djtersteegc/fujinet-appleii-hardware/docs/SmartPort-IIC-Back.jpg

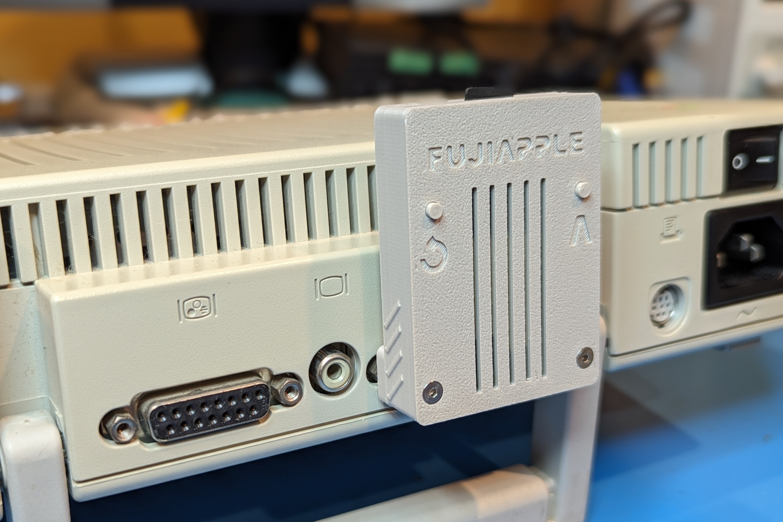
docs/SmartPort-IIC-Back.jpg
