djtersteegc/fujinet-appleii-hardware/docs/SmartPort-IIGS.jpg

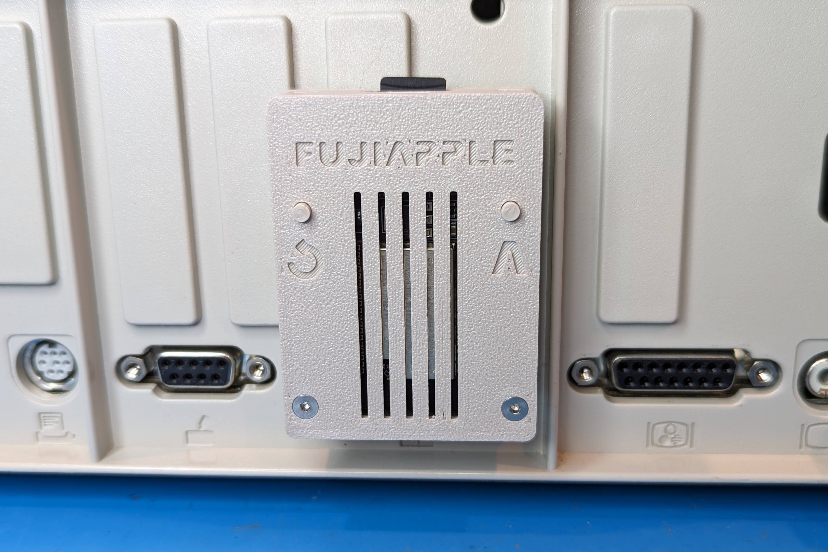
docs/SmartPort-IIGS.jpg
