djtersteegc/fujinet-appleii-hardware/docs/SmartPort-Disassembled.jpg

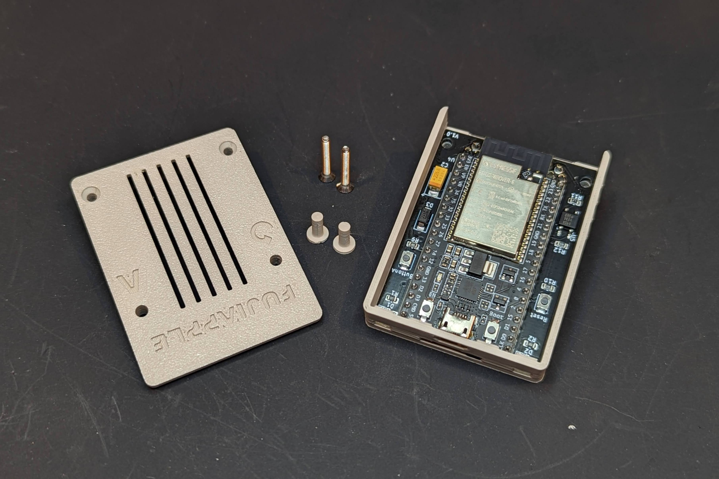
docs/SmartPort-Disassembled.jpg
